medo64/LongwaveTime/Firmware/src/system.h

#pragma once


// CONFIG1
#pragma config FOSC     = INTOSC    // INTOSC oscillator: I/O function on CLKIN pin
#pragma config WDTE     = OFF       // WDT disabled
#pragma config PWRTE    = ON        // PWRT enabled
#pragma config MCLRE    = OFF       // MCLR/VPP pin function is digital input
#pragma config CP       = OFF       // Program memory code protection is disabled
#pragma config BOREN    = ON        // Brown-out Reset enabled
#pragma config CLKOUTEN = OFF       // CLKOUT function is disabled. I/O or oscillator function on the CLKOUT pin
#pragma config IESO     = OFF       // Internal/External Switchover Mode is disabled
#pragma config FCMEN    = OFF       // Fail-Safe Clock Monitor is disabled

// CONFIG2
#pragma config WRT      = OFF       // Write protection off
#pragma config CPUDIV   = NOCLKDIV  // NO CPU system divide
#pragma config USBLSCLK = 48MHz     // System clock expects 48 MHz, FS/LS USB CLKENs divide-by is set to 8
#pragma config PLLMULT  = 3x        // 3x Output Frequency Selected
#pragma config PLLEN    = ENABLED   // 3x or 4x PLL Enabled
#pragma config STVREN   = ON        // Stack Overflow or Underflow will cause a Reset
#pragma config BORV     = LO        // Brown-out Reset Voltage (Vbor), low trip point selected.
#pragma config LPBOR    = OFF       // Low-Power BOR is disabled
#pragma config LVP      = OFF       // High-voltage on MCLR/VPP must be used for programming


#define _XTAL_FREQ 48000000


#define interruptsEnable()   GIE = 1
#define interruptsDisable()  GIE = 0

#define reset()  asm("RESET");
#define wait_short()  __delay_ms(79);


void init(void);
