medo64/LongwaveTime/Firmware/src/system.c

#include <xc.h>
#include <stdint.h>
#include "system.h"


void init(void) {
    interruptsDisable();

    // Oscillator
    OSCCONbits.IRCF = 0b1111;  // 16 MHz or 48 MHz HF
    OSCCONbits.SPLLMULT = 1;   // 3x PLL is enabled
    OSCCONbits.SPLLEN = 1;     // PLL is enabled
    ACTCONbits.ACTSRC = 1;     // The HFINTOSC oscillator is tuned using Fll-speed USB events
    ACTCONbits.ACTEN = 1;      // ACT is enabled, updates to OSCTUNE are exclusive to the ACT
}
