medo64/LongwaveTime/Firmware/src/usb.c

#include <stdbool.h>
#include <stdint.h>
#include "usb.h"


void usb_bufferCopy(uint8_t* destination, const uint8_t* source, const uint8_t count) {
    for (uint8_t i = 0; i < count ; i++) {
        *destination = *source;
        destination++;
        source++;
    }
}
